japz/mysql/Wind Direction Sensor/WINDDIRECTION3DPRINT/Wind-Direction-3DPRINT-Sensor-Wiring-Rev8.png

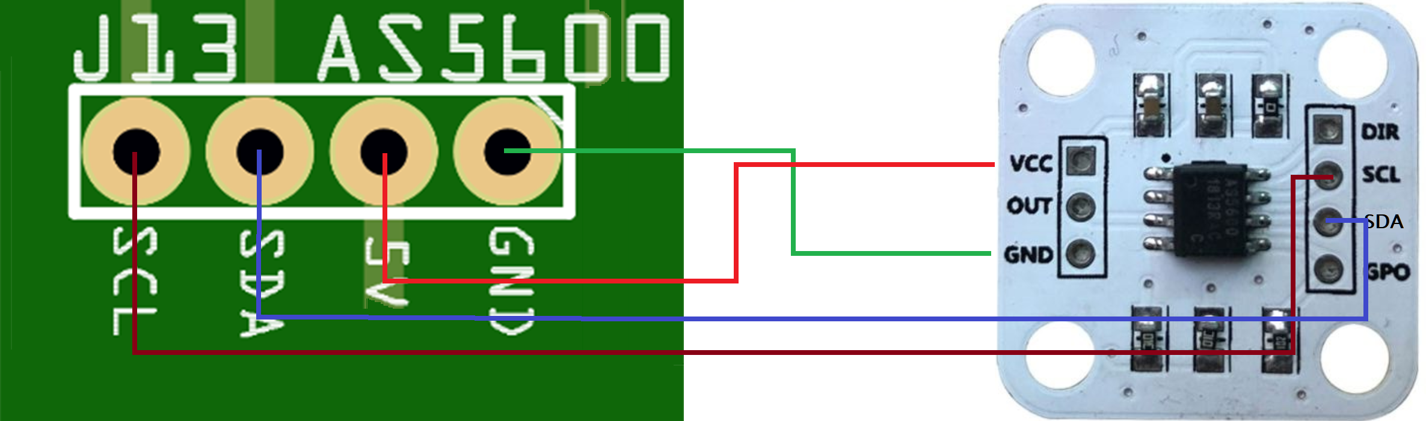
Wind Direction Sensor/WINDDIRECTION3DPRINT/Wind-Direction-3DPRINT-Sensor-Wiring-Rev8.png
