japz/mysql/PCB mySQMPLUS-ESP32/mySQM+ 014_schem.png

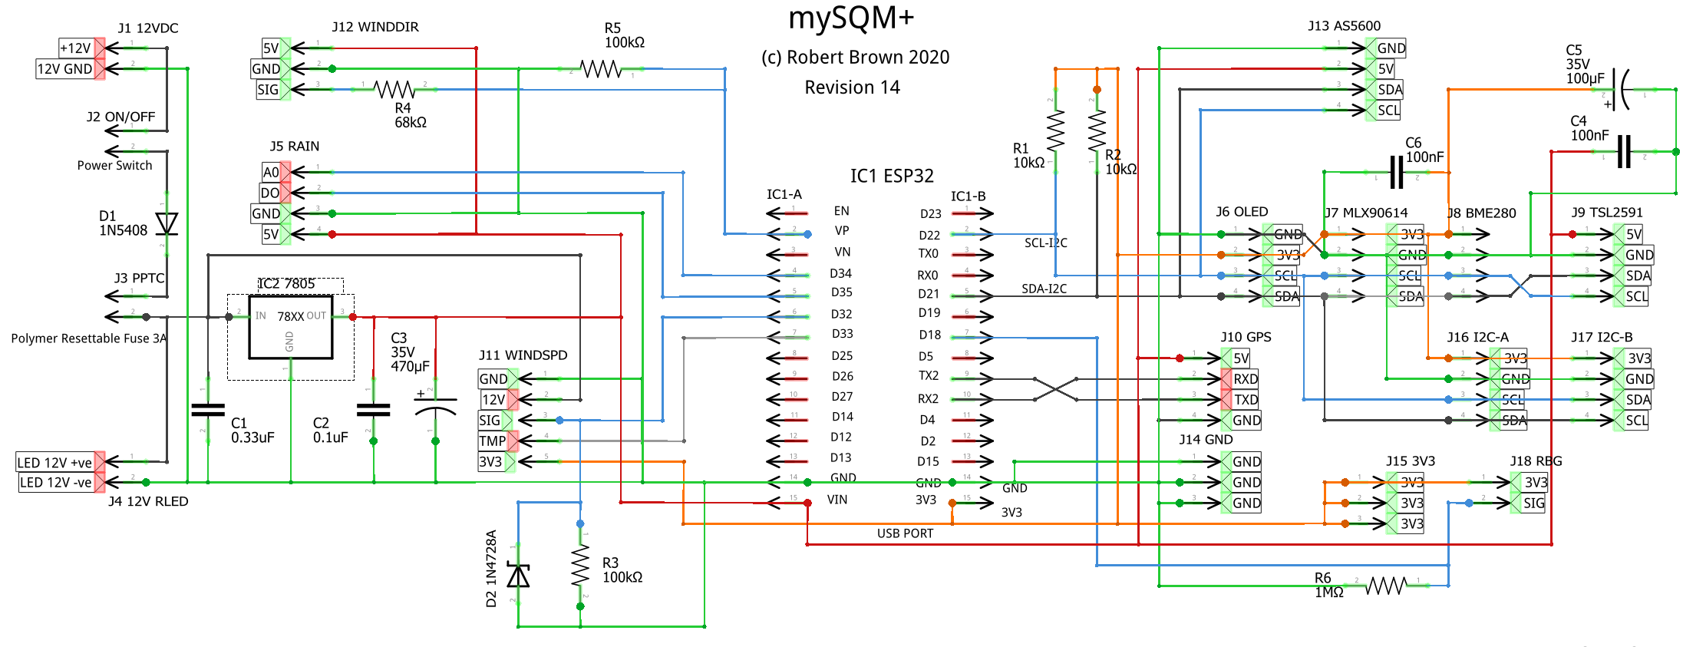
PCB mySQMPLUS-ESP32/mySQM+ 014_schem.png
