japz/mysql/PCB mySQMPLUS-ESP32/mySQM+ Rev14-Top.png

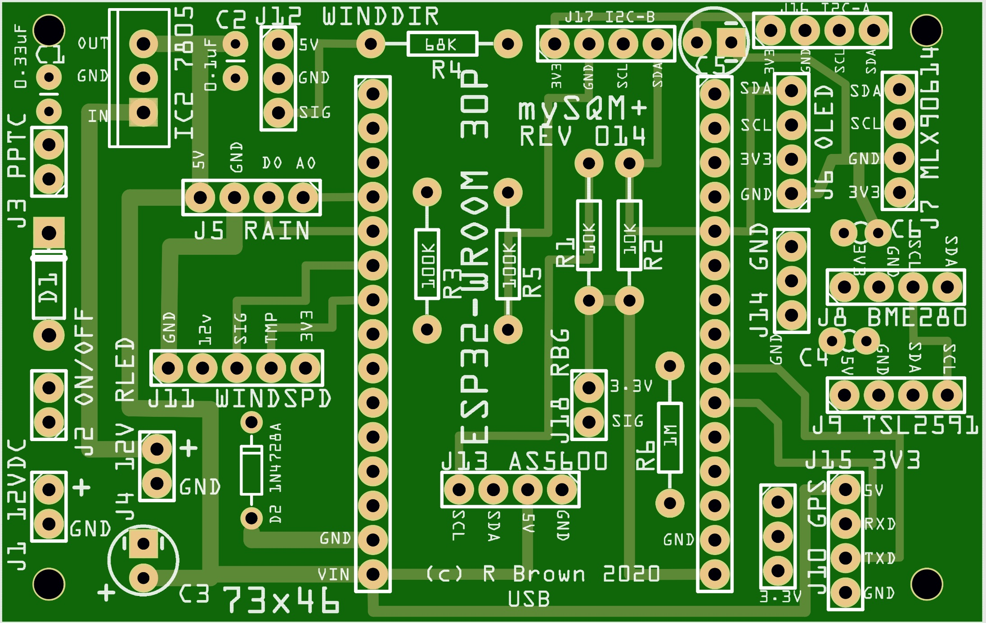
PCB mySQMPLUS-ESP32/mySQM+ Rev14-Top.png
