japz/mysql/Weather Station Misol/Misol WH-SP-WS01.png

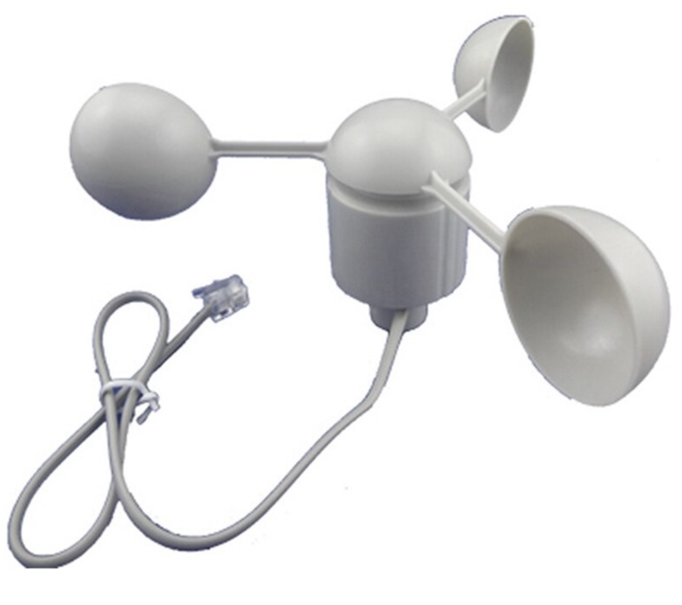
Weather Station Misol/Misol WH-SP-WS01.png
