japz/mysql/Weather Station Misol/WH-SP-WS01 Anemometer Spare Part/weather-station-02.jpg

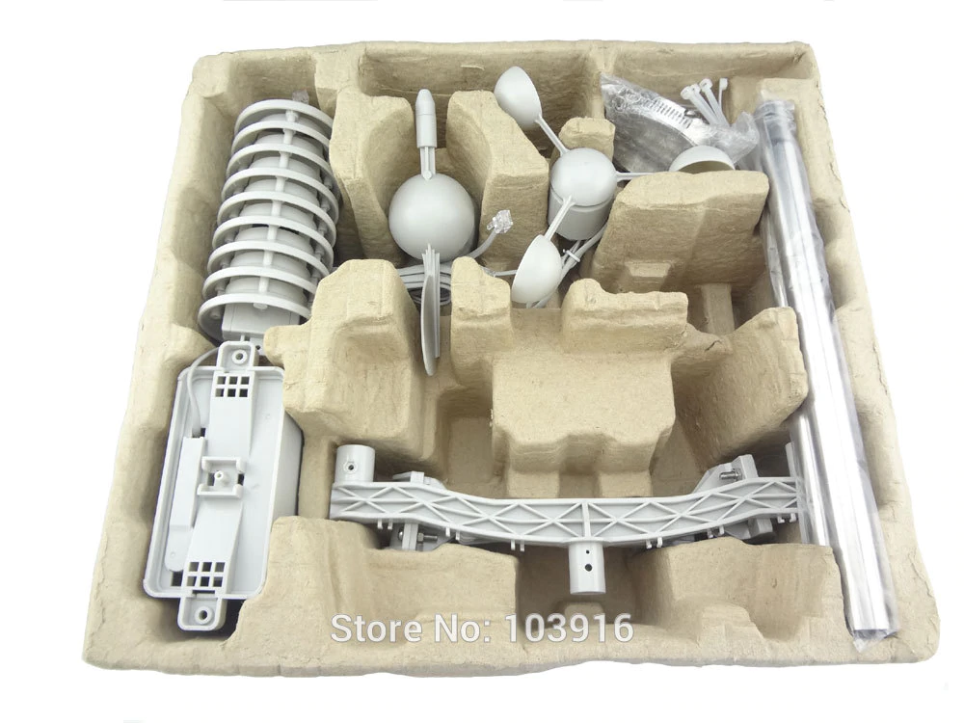
Weather Station Misol/WH-SP-WS01 Anemometer Spare Part/weather-station-02.jpg
