japz/mysql/Wind Direction Sensor/WINDDIRECTION3DPRINT/AS5600 Sensor/AS5600-Dimensions-2.png

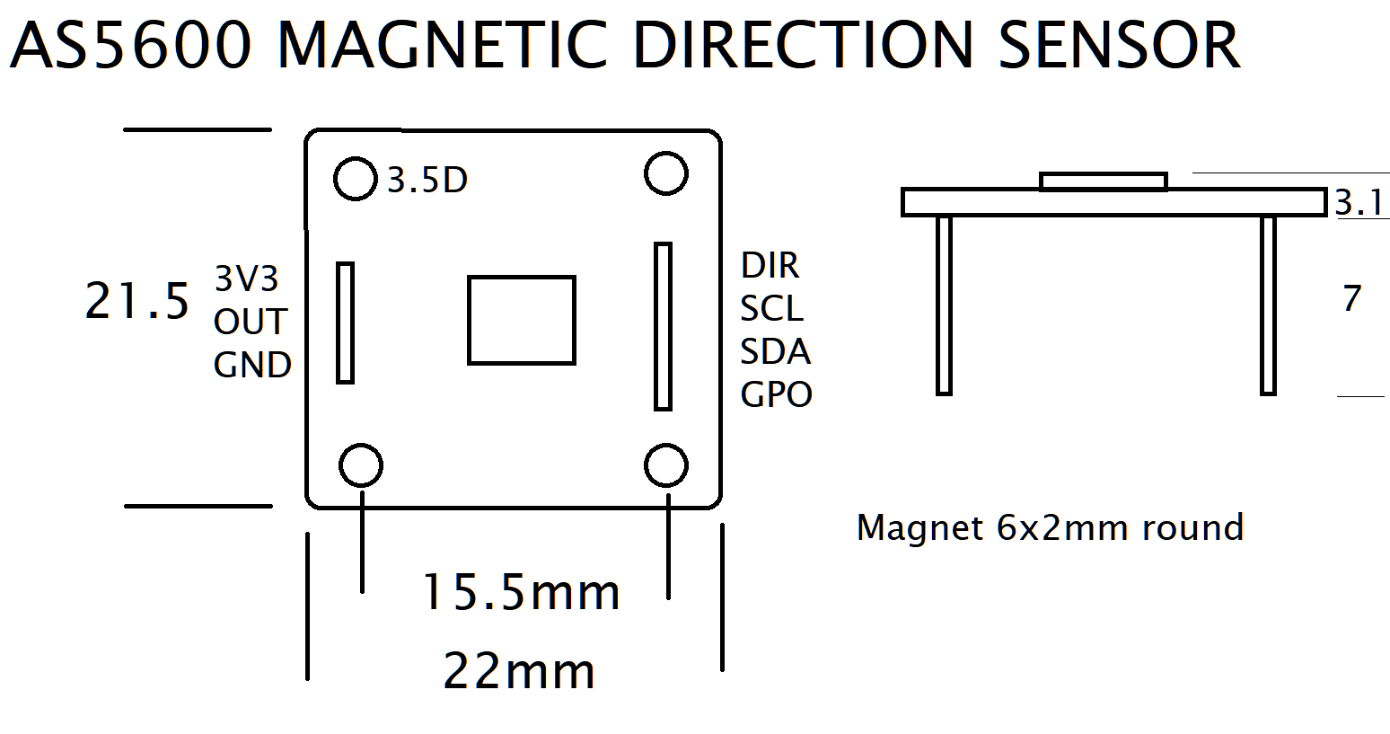
Wind Direction Sensor/WINDDIRECTION3DPRINT/AS5600 Sensor/AS5600-Dimensions-2.png
