japz/mysql/Wind Direction Sensor/WINDDIRECTION3DPRINT/Design/WindPointerFinal-1.jpg

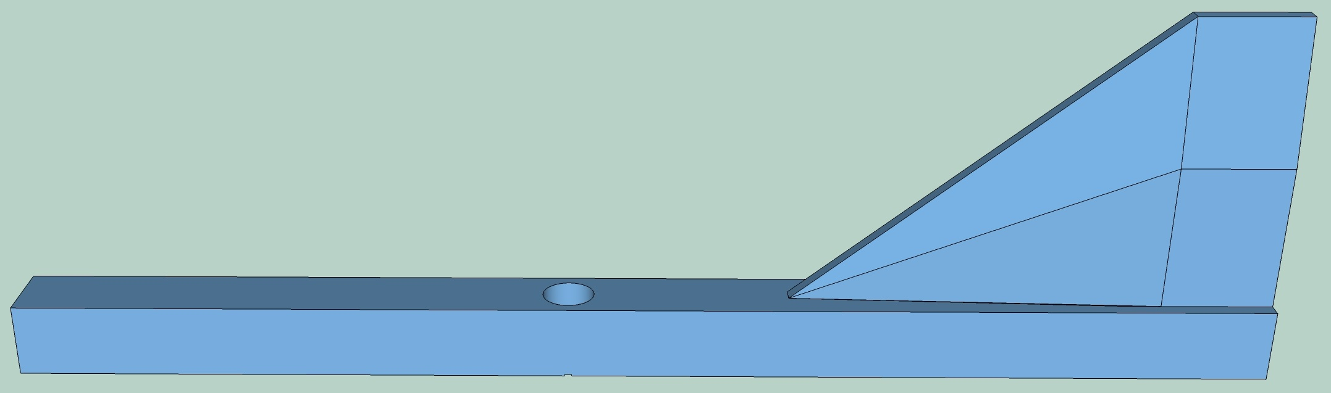
Wind Direction Sensor/WINDDIRECTION3DPRINT/Design/WindPointerFinal-1.jpg
