japz/mysql/Wind Direction Sensor/WINDDIRECTION3DPRINT/Design/WindPointerTip-Final.jpg

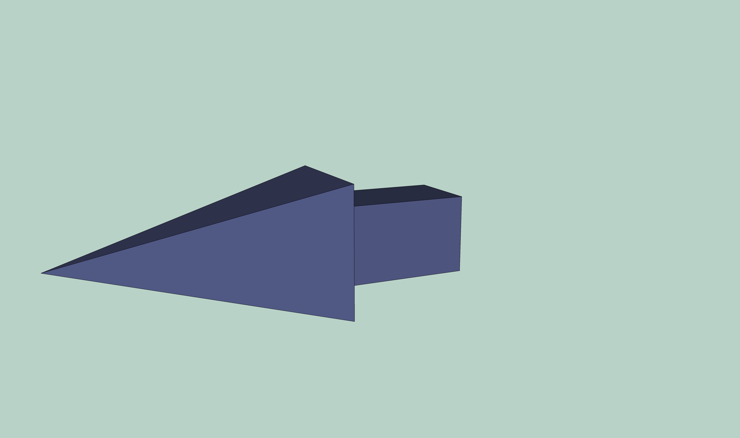
Wind Direction Sensor/WINDDIRECTION3DPRINT/Design/WindPointerTip-Final.jpg
