japz/mysql/Wind Direction Sensor/WINDDIRECTIONANALOG/Resistor-Divider.png

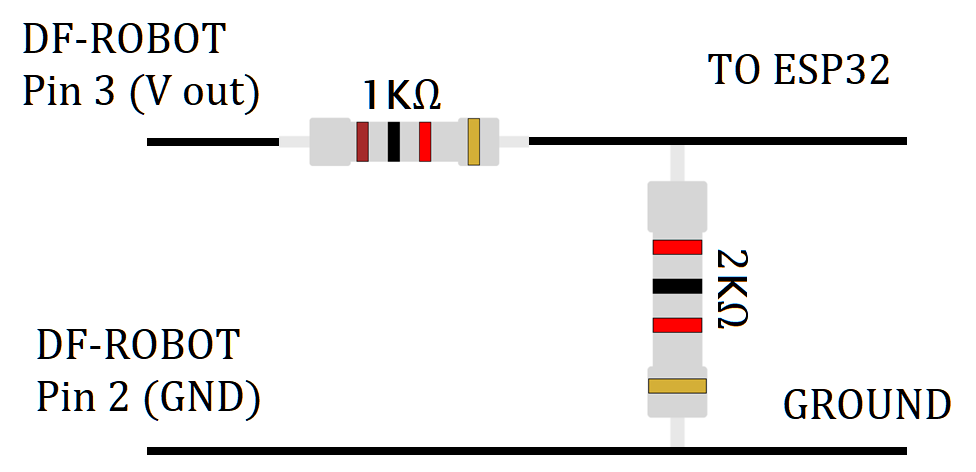
Wind Direction Sensor/WINDDIRECTIONANALOG/Resistor-Divider.png
