japz/mysql/Wind Direction Sensor/WINDDIRECTION3DPRINT/Base-Assembly.png

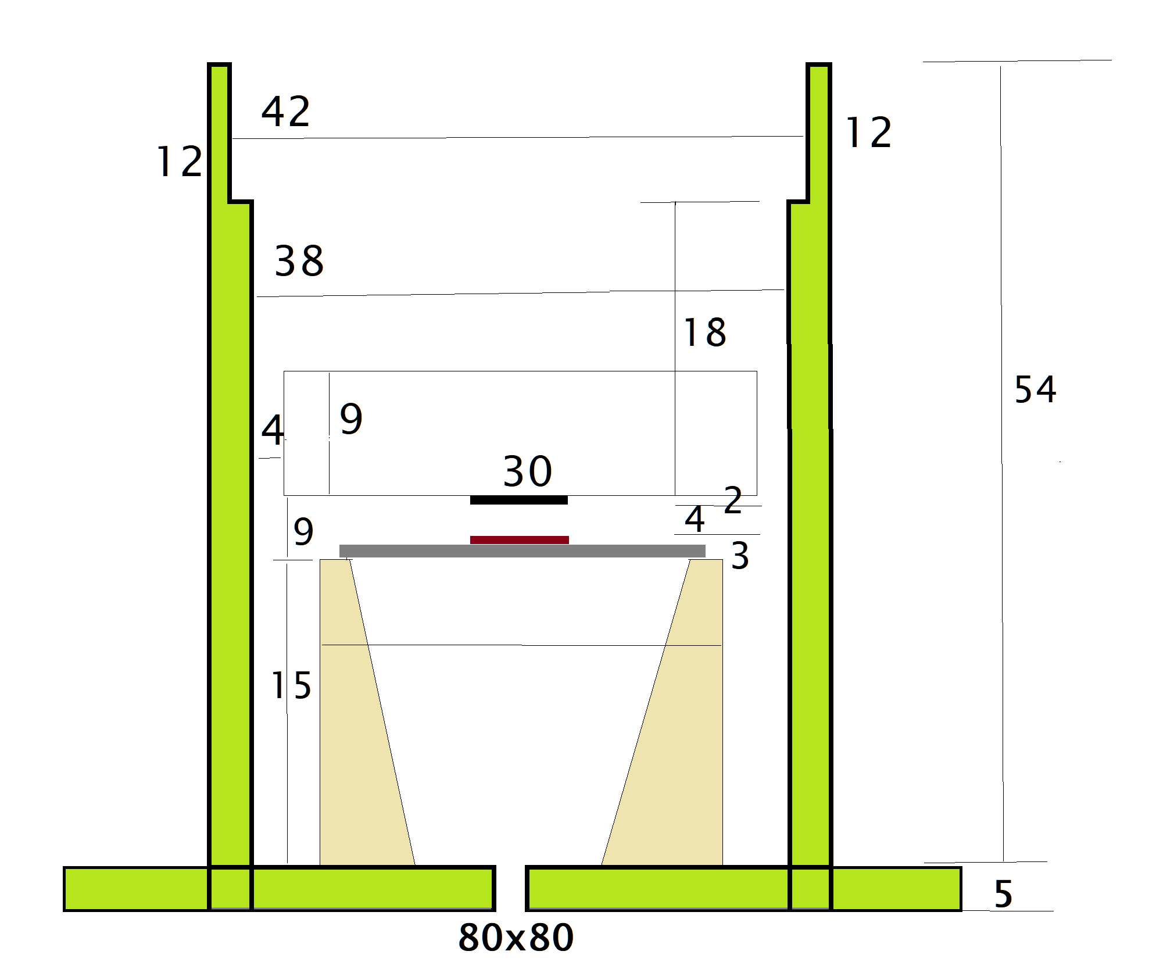
Wind Direction Sensor/WINDDIRECTION3DPRINT/Base-Assembly.png
