japz/mysql/Wind Direction Sensor/WINDDIRECTION3DPRINT/Cover-Assembly.png

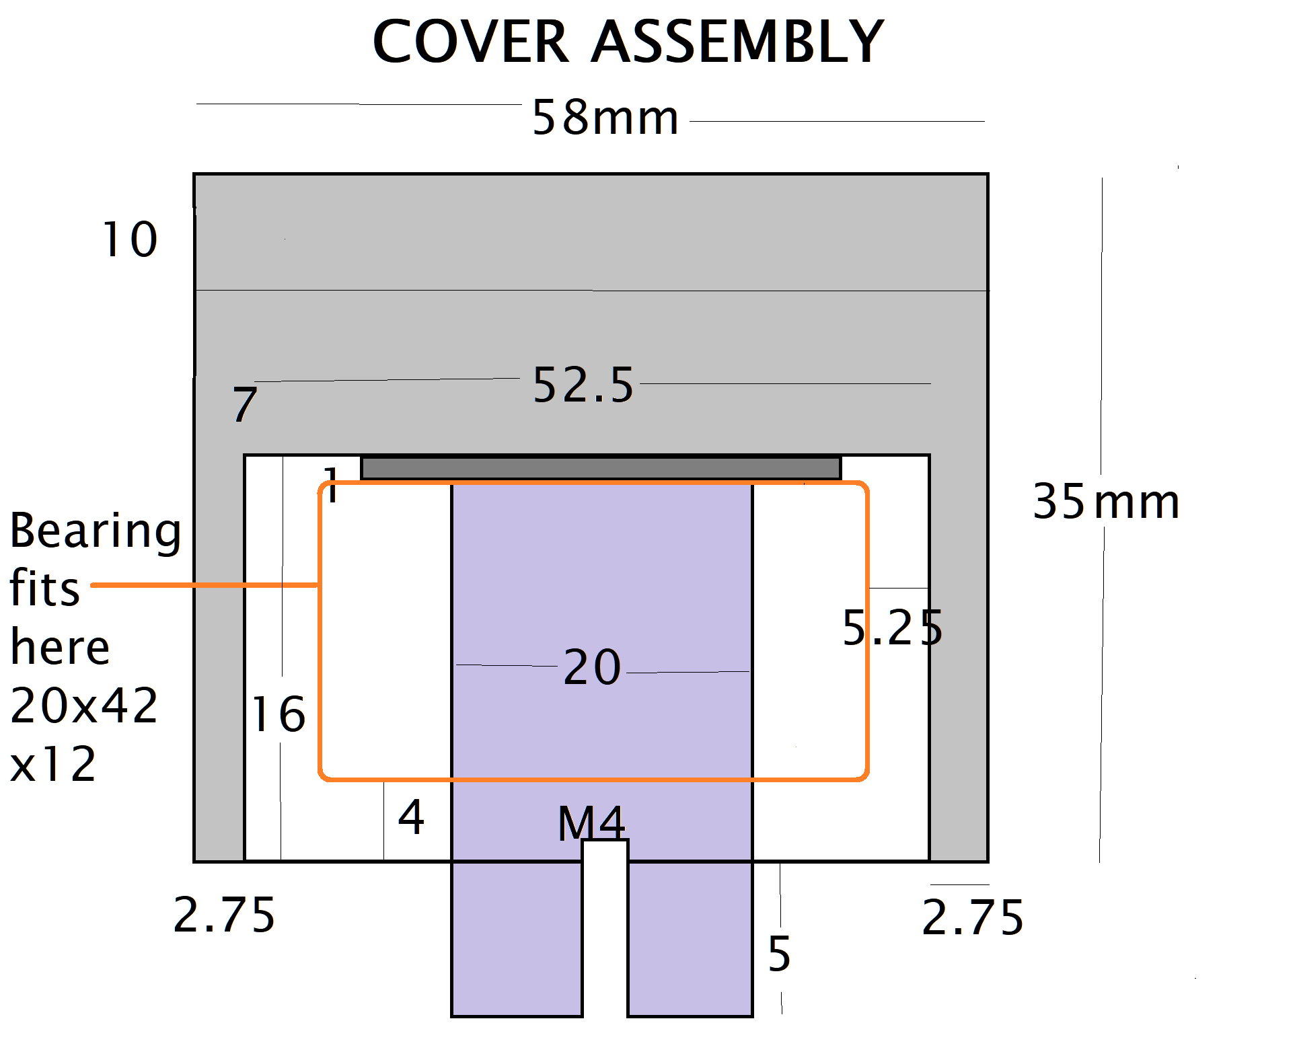
Wind Direction Sensor/WINDDIRECTION3DPRINT/Cover-Assembly.png
