japz/mysql/Wind Direction Sensor/WINDDIRECTION3DPRINT/Lever-Arm-Assembly.png

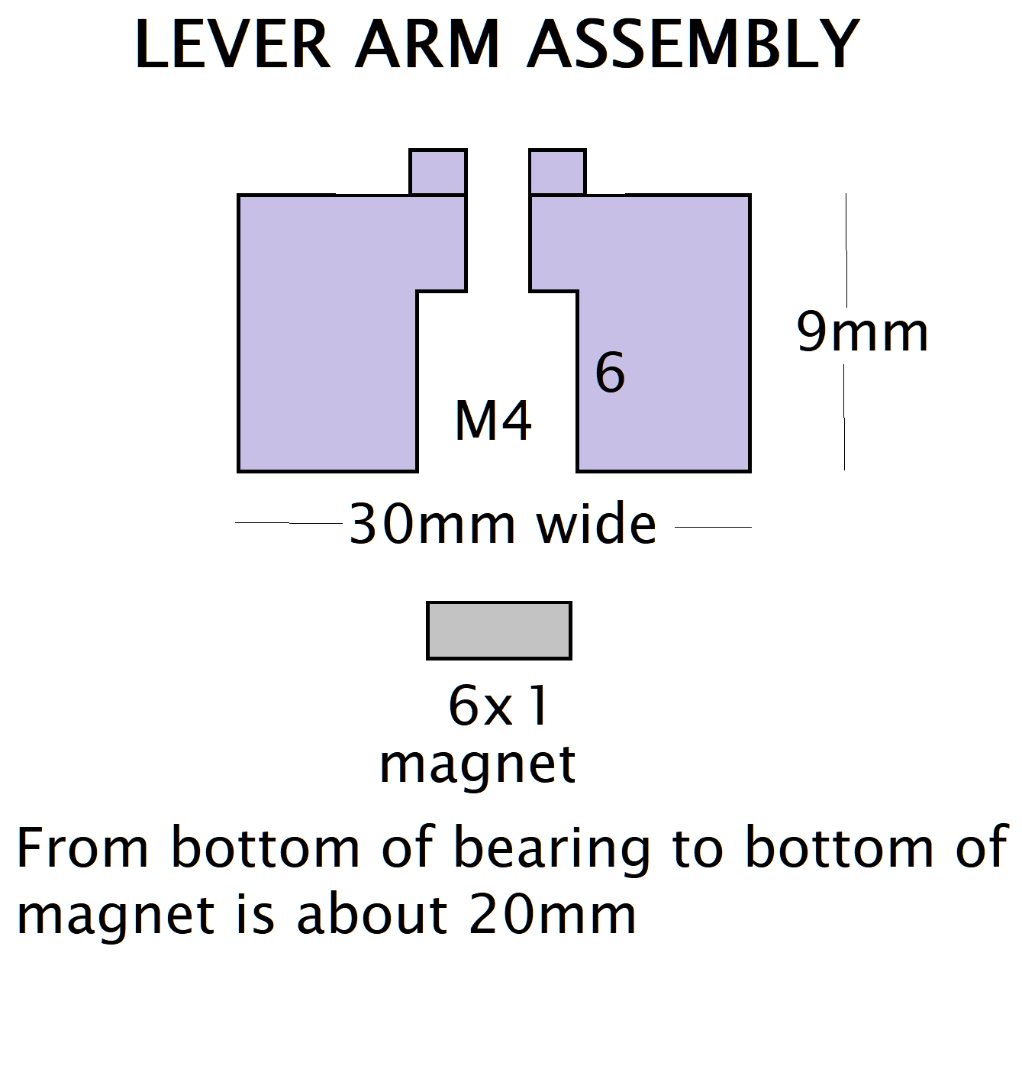
Wind Direction Sensor/WINDDIRECTION3DPRINT/Lever-Arm-Assembly.png
