japz/mysql/Wind Direction Sensor/WINDDIRECTION3DPRINT/Wind-Vane-Assembly.png

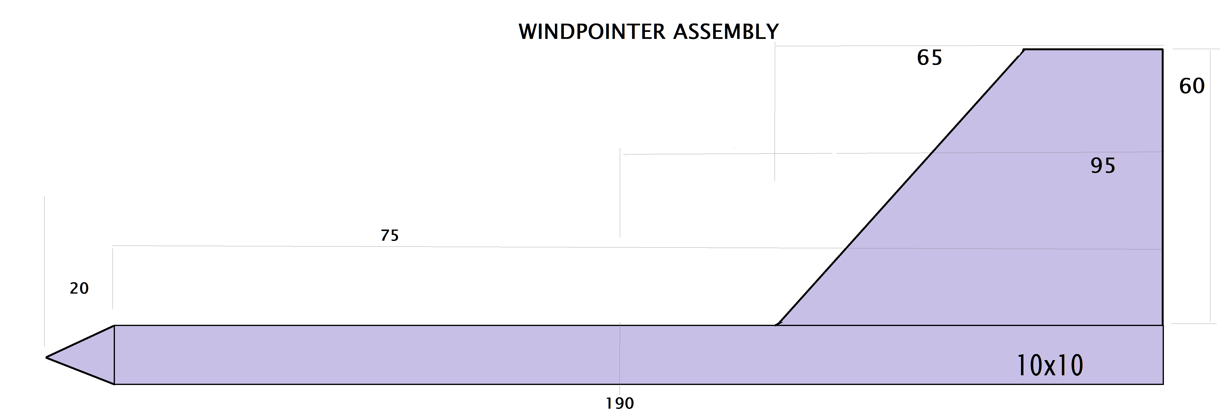
Wind Direction Sensor/WINDDIRECTION3DPRINT/Wind-Vane-Assembly.png
