japz/mysql/Wind Direction Sensor/WINDDIRECTIONANALOG/Liyuan-Wiring.png

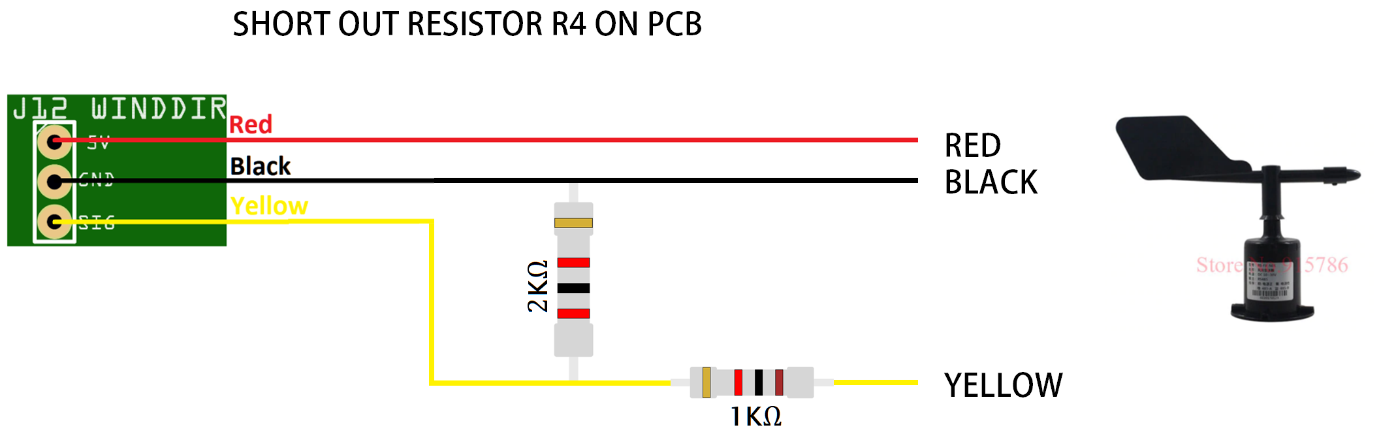
Wind Direction Sensor/WINDDIRECTIONANALOG/Liyuan-Wiring.png
