japz/mysql/Wind Direction Sensor/WINDDIRECTIONANALOG/WINDDIRECTION80422-Wiring.png

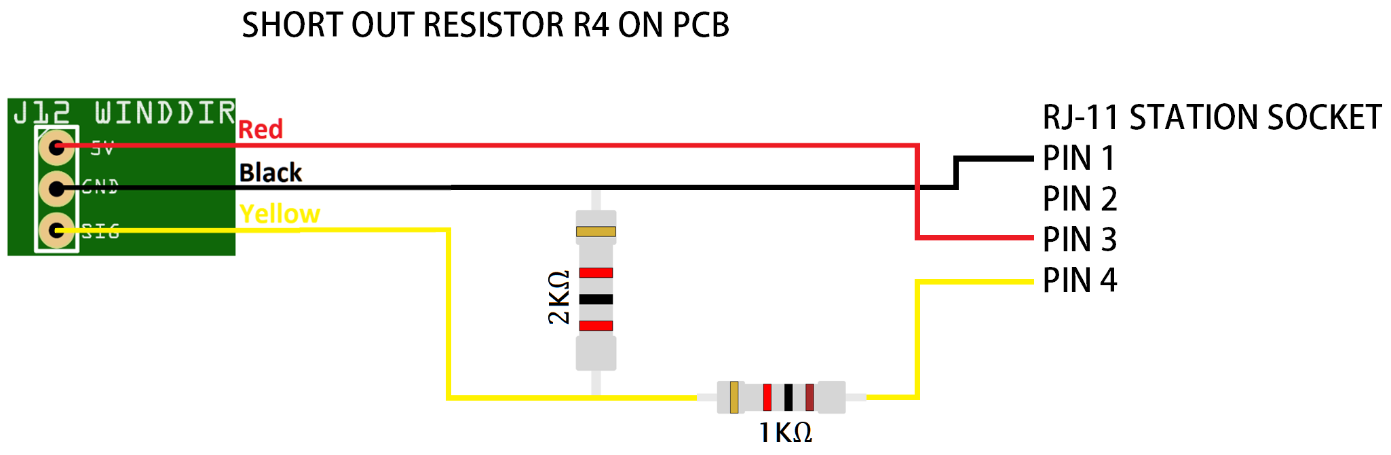
Wind Direction Sensor/WINDDIRECTIONANALOG/WINDDIRECTION80422-Wiring.png
